ep2k/epFC/design/console/apu/mix.sv

module mix (
    input  logic [3:0] pulse1_wave,
    input  logic [3:0] pulse2_wave,
    input  logic [3:0] tri_wave,
    input  logic [3:0] noise_wave,
    input  logic [6:0] dmc_wave,
    input  logic [4:0] mute,

    output logic [8:0] sum_wave
);

    logic [7:0] pulse_table;
    logic [8:0] tnd_table;
    
    logic [4:0] pulse_table_arg;
    logic [7:0] tnd_table_arg;

    logic [3:0] pulse1_wave_eff, pulse2_wave_eff;
    logic [3:0] tri_wave_eff, noise_wave_eff;
    logic [6:0] dmc_wave_eff;
    
    assign pulse1_wave_eff = mute[0] ? 4'h0 : pulse1_wave;
    assign pulse2_wave_eff = mute[1] ? 4'h0 : pulse2_wave;
    assign tri_wave_eff = mute[2] ? 4'h0 : tri_wave;
    assign noise_wave_eff = mute[3] ? 4'h0 : noise_wave;
    assign dmc_wave_eff = mute[4] ? 7'h0 : dmc_wave;

    assign pulse_table_arg = pulse1_wave_eff + pulse2_wave_eff;
    assign tnd_table_arg =
        tri_wave_eff + tri_wave_eff + tri_wave_eff
            + noise_wave_eff + noise_wave_eff + dmc_wave_eff;

    assign sum_wave = pulse_table + tnd_table;

    always_comb begin
        case (pulse_table_arg)
            5'd0: pulse_table = 8'd0;
            5'd1: pulse_table = 8'd6;
            5'd2: pulse_table = 8'd12;
            5'd3: pulse_table = 8'd17;
            5'd4: pulse_table = 8'd23;
            5'd5: pulse_table = 8'd28;
            5'd6: pulse_table = 8'd34;
            5'd7: pulse_table = 8'd39;
            5'd8: pulse_table = 8'd44;
            5'd9: pulse_table = 8'd49;
            5'd10: pulse_table = 8'd53;
            5'd11: pulse_table = 8'd58;
            5'd12: pulse_table = 8'd63;
            5'd13: pulse_table = 8'd67;
            5'd14: pulse_table = 8'd72;
            5'd15: pulse_table = 8'd76;
            5'd16: pulse_table = 8'd80;
            5'd17: pulse_table = 8'd84;
            5'd18: pulse_table = 8'd88;
            5'd19: pulse_table = 8'd92;
            5'd20: pulse_table = 8'd96;
            5'd21: pulse_table = 8'd100;
            5'd22: pulse_table = 8'd104;
            5'd23: pulse_table = 8'd108;
            5'd24: pulse_table = 8'd111;
            5'd25: pulse_table = 8'd115;
            5'd26: pulse_table = 8'd118;
            5'd27: pulse_table = 8'd122;
            5'd28: pulse_table = 8'd125;
            5'd29: pulse_table = 8'd128;
            5'd30: pulse_table = 8'd132;
            default: pulse_table = 8'd0;
        endcase
    end

    always_comb begin
        case (tnd_table_arg)
            8'd0: tnd_table = 9'd0;
            8'd1: tnd_table = 9'd3;
            8'd2: tnd_table = 9'd7;
            8'd3: tnd_table = 9'd10;
            8'd4: tnd_table = 9'd14;
            8'd5: tnd_table = 9'd17;
            8'd6: tnd_table = 9'd20;
            8'd7: tnd_table = 9'd23;
            8'd8: tnd_table = 9'd27;
            8'd9: tnd_table = 9'd30;
            8'd10: tnd_table = 9'd33;
            8'd11: tnd_table = 9'd36;
            8'd12: tnd_table = 9'd39;
            8'd13: tnd_table = 9'd42;
            8'd14: tnd_table = 9'd46;
            8'd15: tnd_table = 9'd49;
            8'd16: tnd_table = 9'd52;
            8'd17: tnd_table = 9'd55;
            8'd18: tnd_table = 9'd58;
            8'd19: tnd_table = 9'd61;
            8'd20: tnd_table = 9'd64;
            8'd21: tnd_table = 9'd66;
            8'd22: tnd_table = 9'd69;
            8'd23: tnd_table = 9'd72;
            8'd24: tnd_table = 9'd75;
            8'd25: tnd_table = 9'd78;
            8'd26: tnd_table = 9'd81;
            8'd27: tnd_table = 9'd84;
            8'd28: tnd_table = 9'd86;
            8'd29: tnd_table = 9'd89;
            8'd30: tnd_table = 9'd92;
            8'd31: tnd_table = 9'd95;
            8'd32: tnd_table = 9'd97;
            8'd33: tnd_table = 9'd100;
            8'd34: tnd_table = 9'd103;
            8'd35: tnd_table = 9'd105;
            8'd36: tnd_table = 9'd108;
            8'd37: tnd_table = 9'd110;
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
            8'd198: tnd_table = 9'd375;
            8'd199: tnd_table = 9'd376;
            8'd200: tnd_table = 9'd377;
            8'd201: tnd_table = 9'd378;
            8'd202: tnd_table = 9'd379;
            default: tnd_table = 9'd0;
        endcase
    end

endmodule
