ep2k/epFC/design/seg7_buttons.sv

module seg7_buttons (
    input  logic [7:0] buttons,
    input  logic no_push_pwm,
    output logic [6:0] odat_l,
    output logic [6:0] odat_r
);

    assign odat_l = ~{
        buttons[5] | no_push_pwm,   // ↓
        buttons[6] | no_push_pwm,   // ←
        1'b0,
        buttons[2] | no_push_pwm,   // Select
        1'b0,
        buttons[7] | no_push_pwm,   // →
        buttons[4] | no_push_pwm    // ↑
    };

    assign odat_r = ~{
        buttons[1] | no_push_pwm,   // B
        1'b0,
        1'b0,
        buttons[3] | no_push_pwm,   // Start
        1'b0,
        buttons[0] | no_push_pwm,   // A
        1'b0
    };
    
endmodule
